rrainey/DSKY-matic/images/20200926_113404.jpg

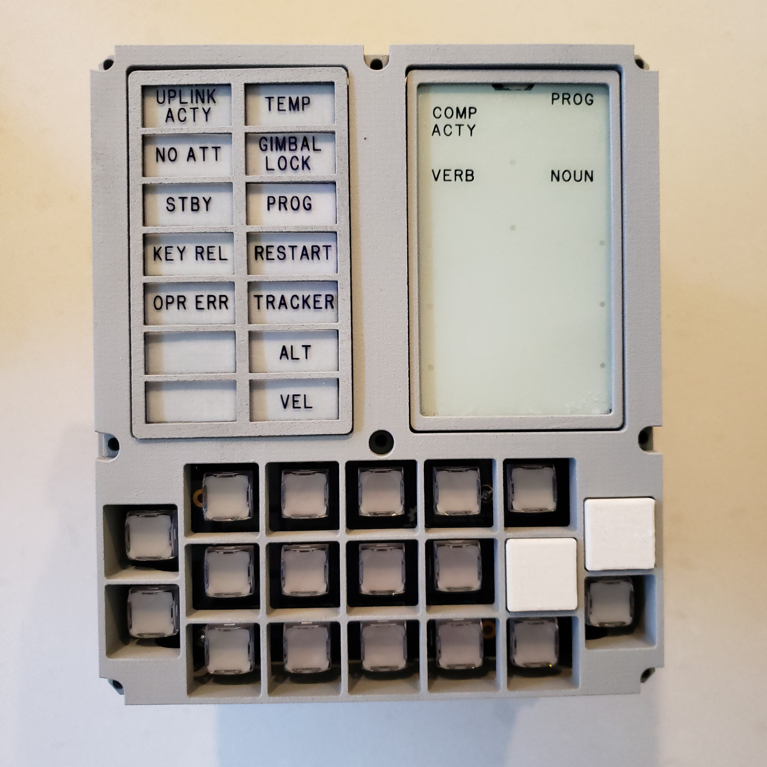
images/20200926_113404.jpg
