rrainey/DSKY-matic/images/20200926_113407.jpg

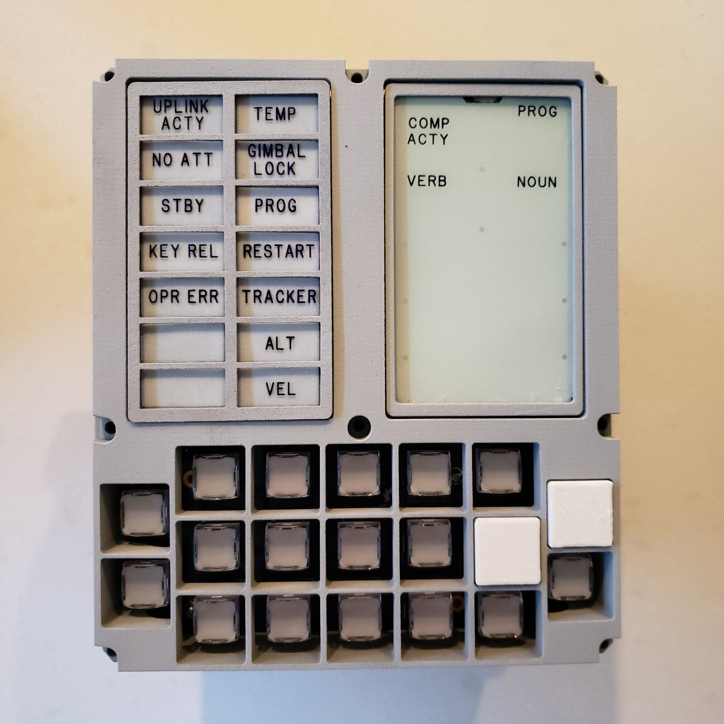
images/20200926_113407.jpg
