rrainey/DSKY-matic/images/20200926_113521.jpg

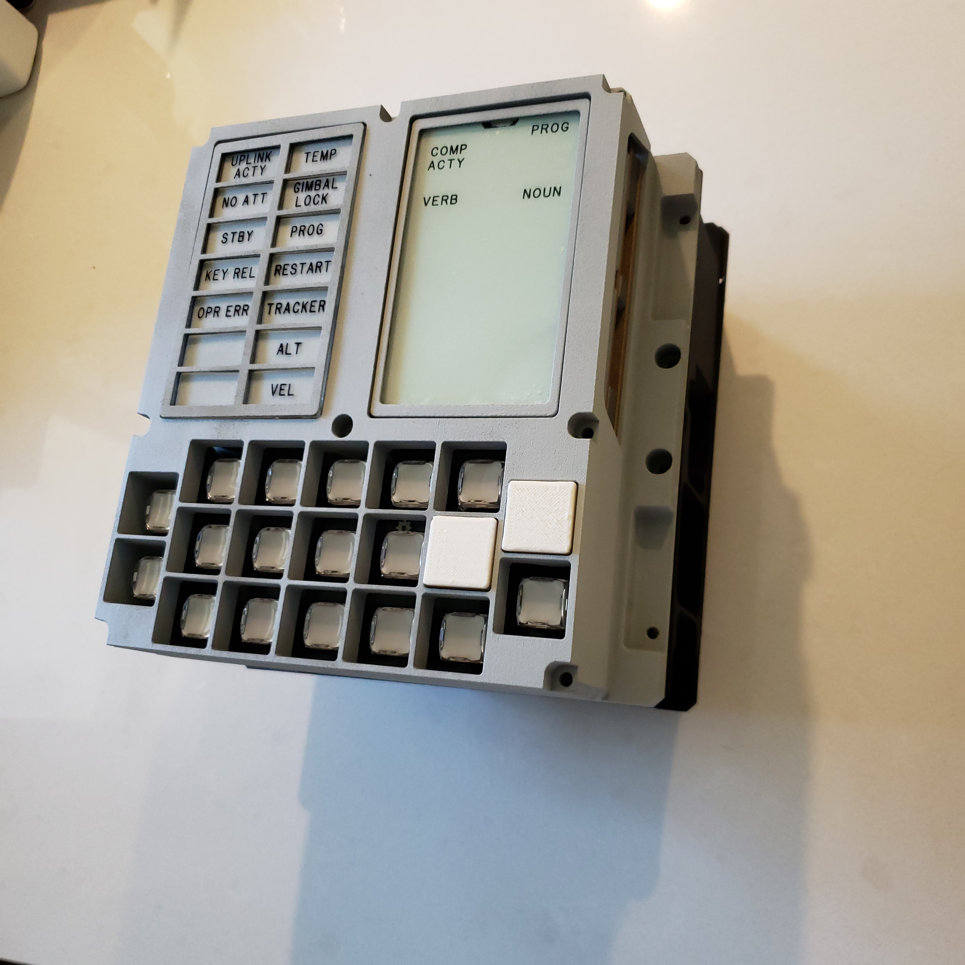
images/20200926_113521.jpg
