rrainey/DSKY-matic/images/20200926_113555.jpg

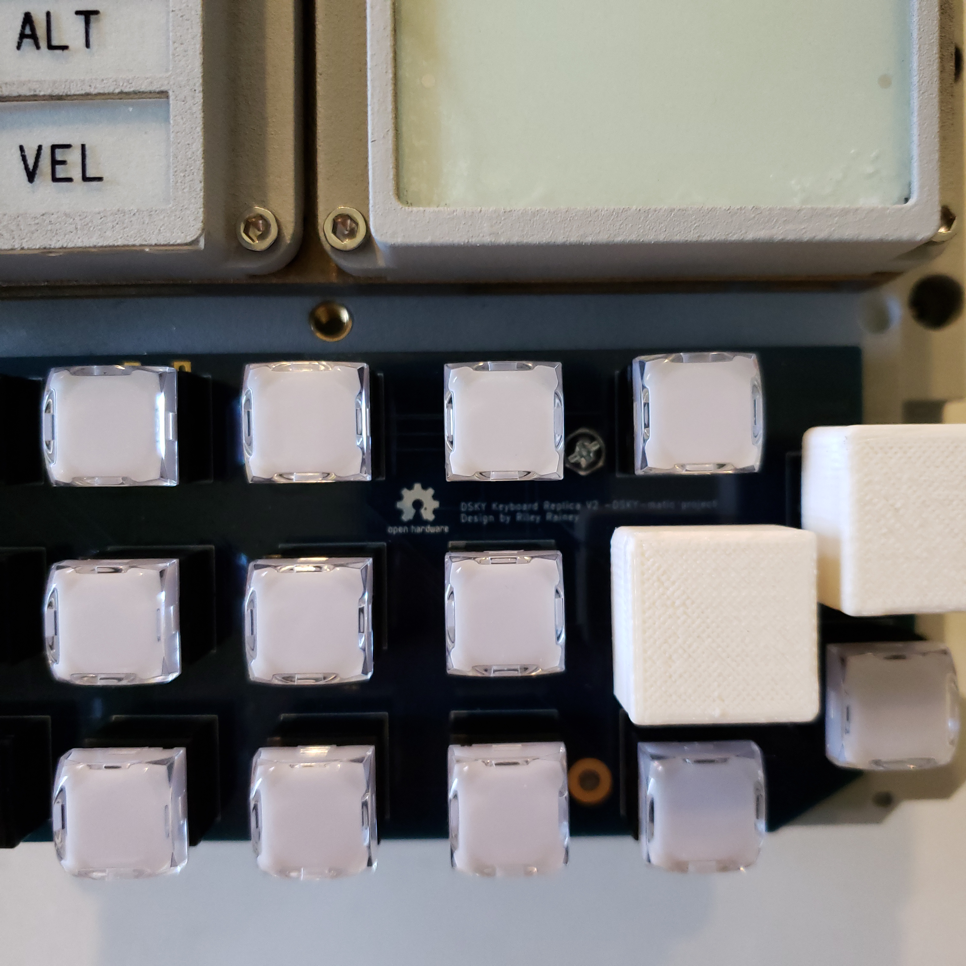
images/20200926_113555.jpg
