rrainey/DSKY-matic/images/20200926_113603.jpg

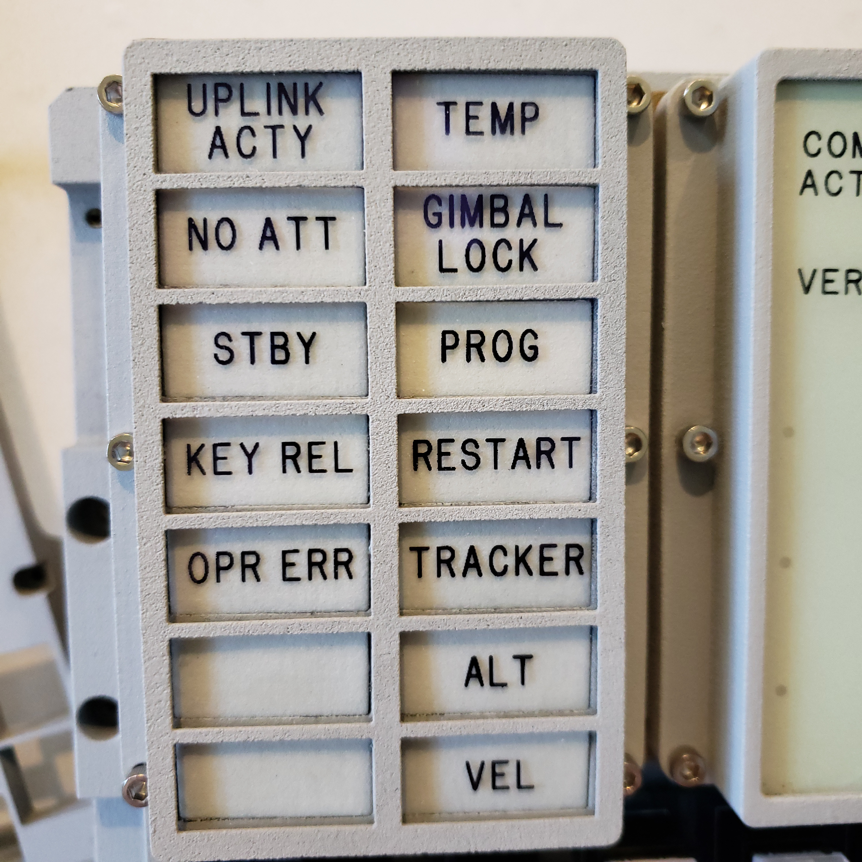
images/20200926_113603.jpg
