rrainey/DSKY-matic/images/20200926_113609.jpg

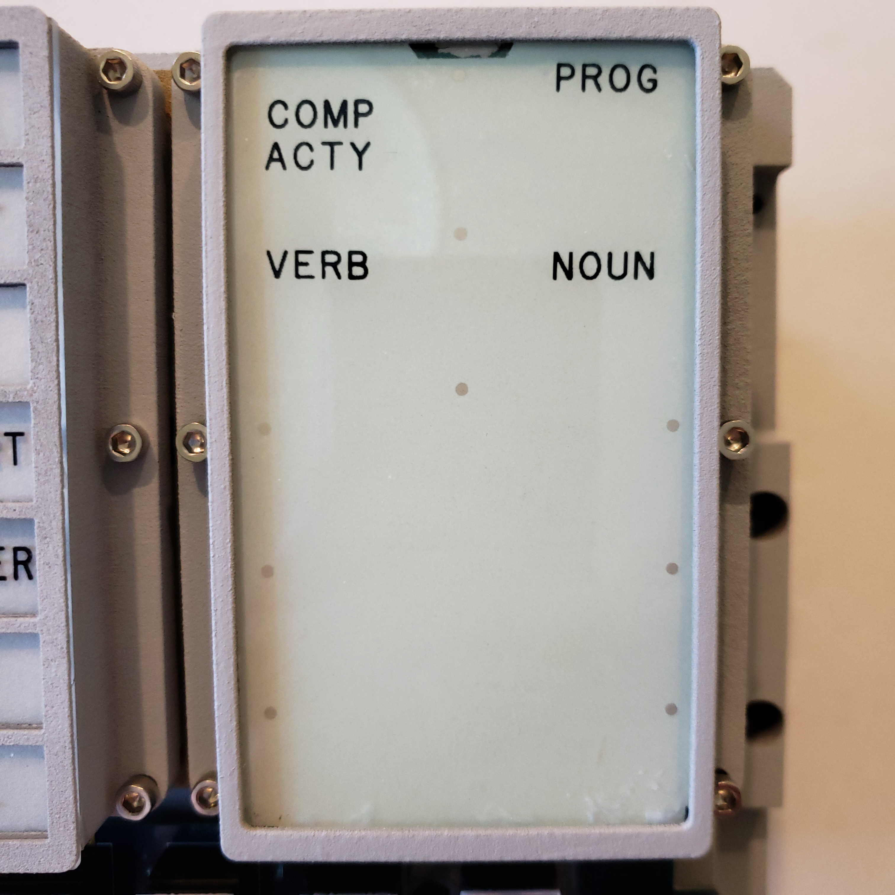
images/20200926_113609.jpg
