rrainey/DSKY-matic/images/cover-off-02.jpg

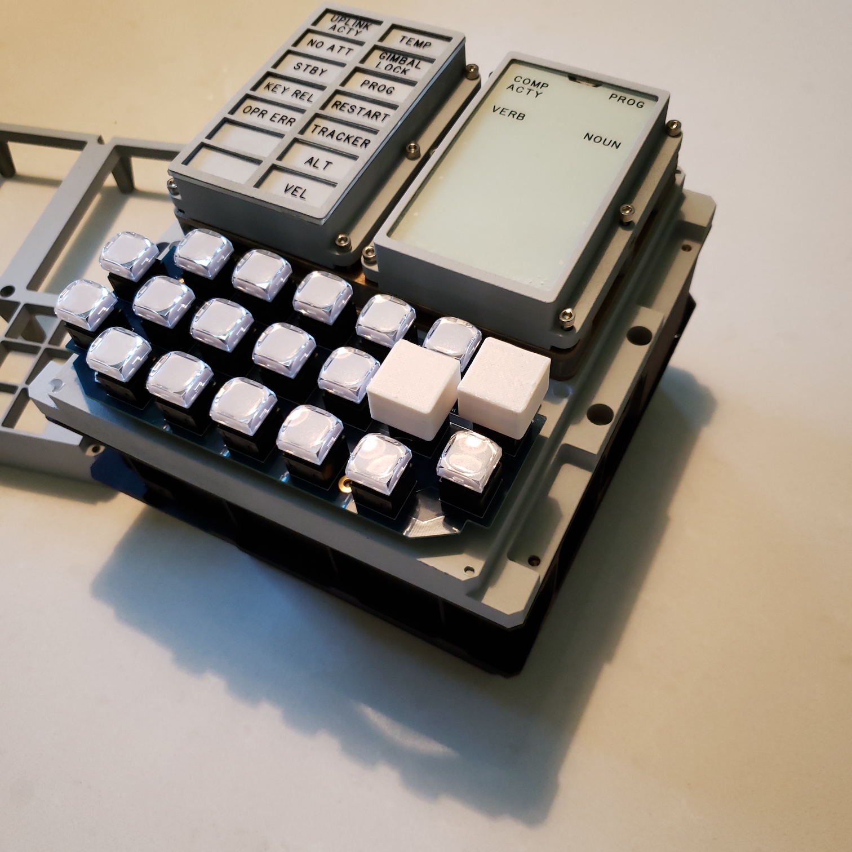
images/cover-off-02.jpg
