rrainey/DSKY-matic/images/FDAI-sphere-texture.png

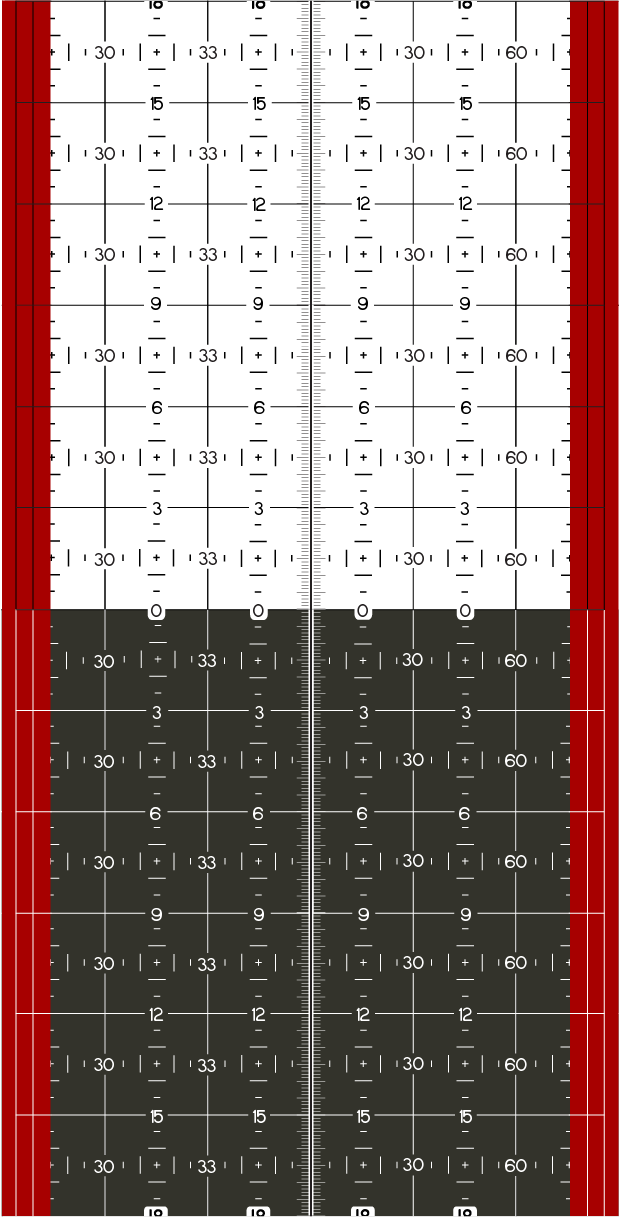
images/FDAI-sphere-texture.png
